MykolaKovalchuk/psion5arm/Images/PXL_20250928_071907219.jpg

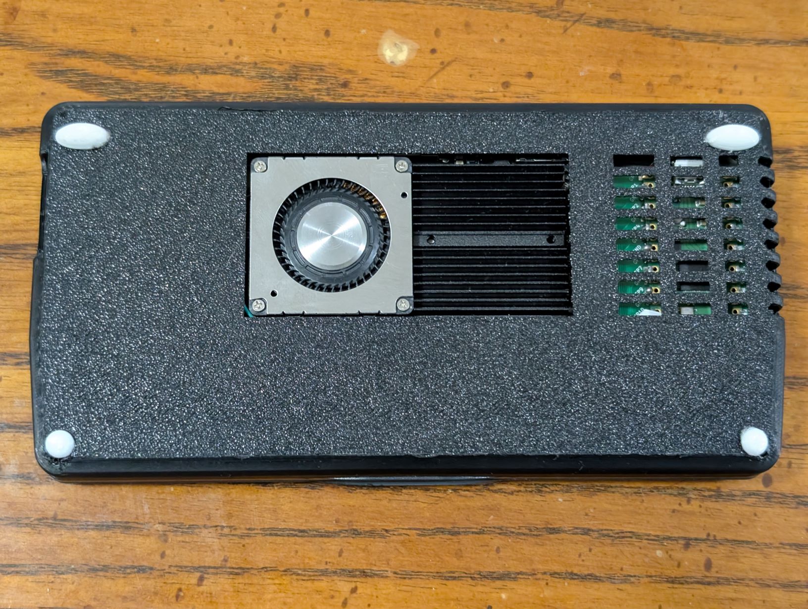
Images/PXL_20250928_071907219.jpg
