MykolaKovalchuk/psion5arm/Images/PXL_20250928_071921942.jpg

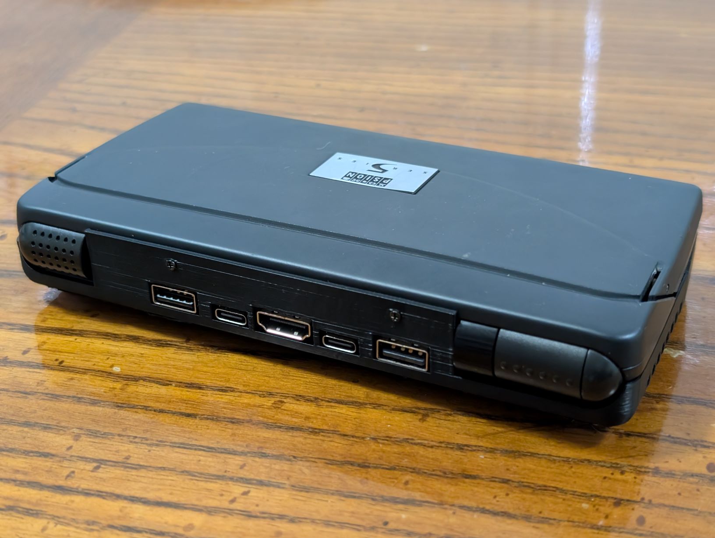
Images/PXL_20250928_071921942.jpg
