MykolaKovalchuk/psion5arm/Images/PXL_20250928_072232430.jpg

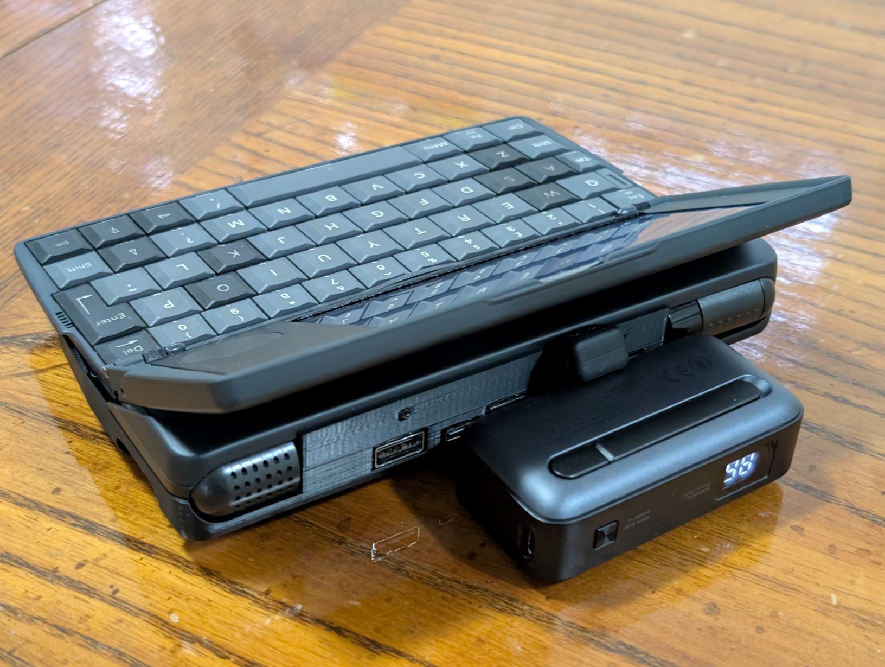
Images/PXL_20250928_072232430.jpg
