MykolaKovalchuk/psion5arm/Images/PXL_20250928_074744058.jpg

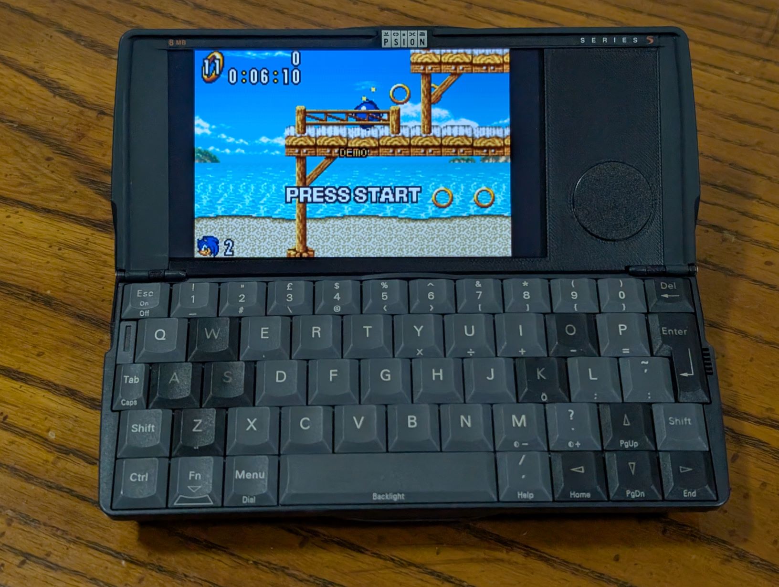
Images/PXL_20250928_074744058.jpg
